Taialt97/OPENBLOCK-Keyboard-Hitbox/FightStick_Beta/FightStickMini.LowProfile/Kicad Files/Untitled.kicad_sch

## KiCad design FightStick_Beta/FightStickMini.LowProfile/Kicad Files/Untitled.kicad_sch (2023-09-11)

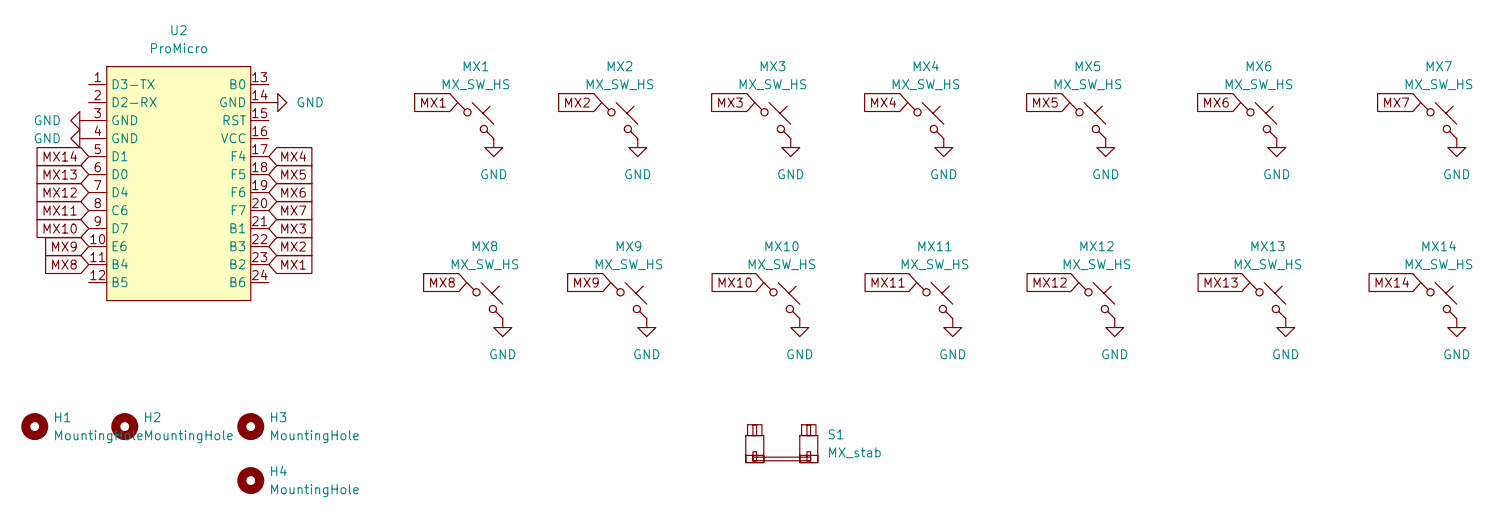
[picture p15: schematic Untitled.kicad_sch]

Parts:
H1, H2, H3, H4: MountingHole; MountingHole_2.2mm_M2_DIN965_Pad
MX1, MX2, MX3, MX4, MX5, MX6, MX7, MX8, MX9, MX10, MX11, MX12, MX13, MX14: MX_SW_HS; Kailh_socket_PG1350_optional
S1: MX_stab; STAB_MX_P_6.25u
U2: ProMicro; Elite-C_ACH

Connections:
GND: MX1.2, MX2.2, MX3.2, MX4.2, MX5.2, MX6.2, MX7.2, MX8.2, MX9.2, MX10.2, MX11.2, MX12.2, MX13.2, MX14.2, U2.3 (GND), U2.4 (GND), U2.14 (GND)
MX1: MX1.1, U2.23 (B2)
MX2: MX2.1, U2.22 (B3)
MX3: MX3.1, U2.21 (B1)
MX4: MX4.1, U2.17 (F4)
MX5: MX5.1, U2.18 (F5)
MX6: MX6.1, U2.19 (F6)
MX7: MX7.1, U2.20 (F7)
MX8: MX8.1, U2.11 (B4)
MX9: MX9.1, U2.10 (E6)
MX10: MX10.1, U2.9 (D7)
MX11: MX11.1, U2.8 (C6)
MX12: MX12.1, U2.7 (D4)
MX13: MX13.1, U2.6 (D0)
MX14: MX14.1, U2.5 (D1)
